yuburoll/modubu/images/modubu16x9.jpg

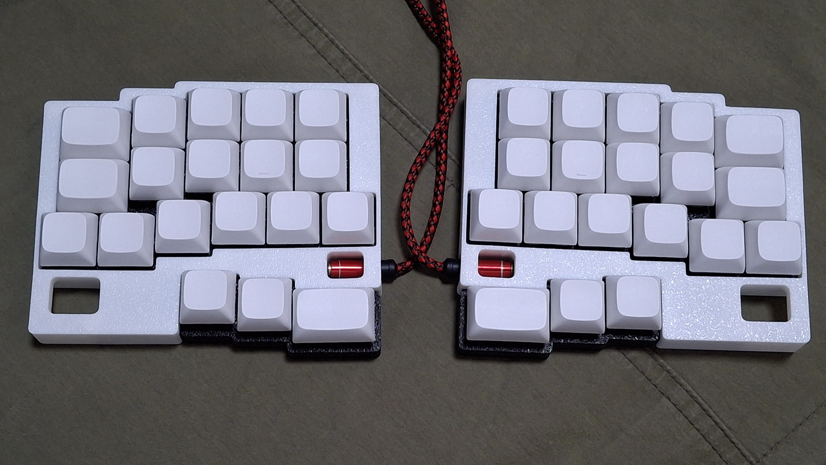
images/modubu16x9.jpg
