yuburoll/modubu/case/stl/leafspringCase/modubuLeafspring_Rplate.stl

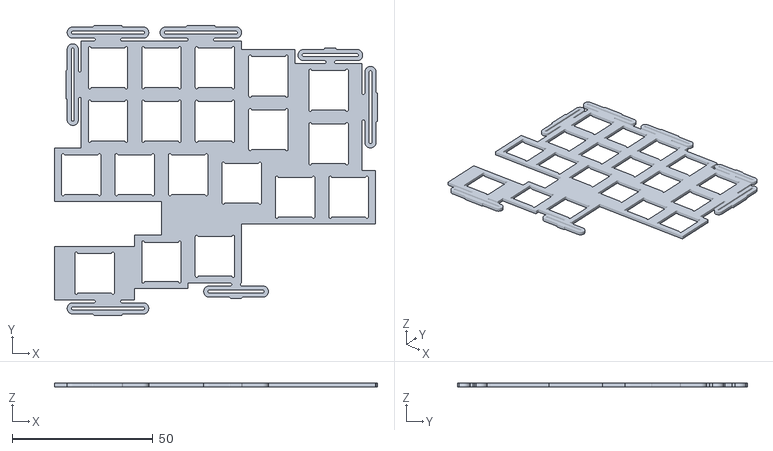
[picture p16: CAD file, 2025-12-07]
case/stl/leafspringCase/modubuLeafspring_Rplate.stl
114.8 x 103.0 x 1.50
